h4km4k/esp_frequency-converter_controller/Esp32/favicon.h

#ifndef FAVICON_H
#define FAVICON_H

#include <stdint.h>
#include <pgmspace.h>

const uint8_t favicon_png[] PROGMEM = {
0x89, 0x50, 0x4E, 0x47, 0x0D, 0x0A, 0x1A, 0x0A, 0x00, 0x00, 0x00, 0x0D, 0x49, 0x48, 0x44, 0x52, 
0x00, 0x00, 0x00, 0xC0, 0x00, 0x00, 0x00, 0xC0, 0x08, 0x06, 0x00, 0x00, 0x00, 0x52, 0xDC, 0x6C, 
0x07, 0x00, 0x00, 0x1A, 0x24, 0x49, 0x44, 0x41, 0x54, 0x78, 0x5E, 0xED, 0x9D, 0x09, 0x78, 0x14, 
0x45, 0xFA, 0x87, 0x7F, 0x95, 0x73, 0x72, 0xDF, 0xF7, 0xC1, 0x91, 0x84, 0x40, 0x08, 0x88, 0xB6, 
0xBB, 0x02, 0x23, 0x02, 0x72, 0x23, 0xA0, 0x03, 0x4C, 0x70, 0x55, 0xC4, 0x1B, 0x2F, 0x76, 0xD7, 
0x7B, 0xFF, 0xAB, 0xAE, 0xEC, 0xBA, 0x2E, 0x2A, 0xA2, 0xAB, 0x5C, 0x8B, 0x08, 0x12, 0x59, 0x58, 
0xC8, 0x40, 0x7B, 0x8C, 0x1C, 0x82, 0xE7, 0x8A, 0x07, 0xBB, 0xDA, 0xB8, 0x28, 0x67, 0x06, 0x88, 
0x10, 0x42, 0x98, 0x10, 0xC8, 0x9D, 0xC9, 0x35, 0xFD, 0x7F, 0xBA, 0x43, 0x34, 0x38, 0x9D, 0xCC, 
0x24, 0x99, 0x49, 0x57, 0xD2, 0xF5, 0x3E, 0x4F, 0x9E, 0x89, 0x32, 0x99, 0xA9, 0xFE, 0xBA, 0xDE, 
0xFE, 0xAA, 0xAA, 0xAB, 0xAA, 0x09, 0x3A, 0x80, 0x08, 0x91, 0xC0, 0x68, 0x0A, 0x45, 0xA3, 0x3D, 
0x0E, 0xBE, 0x64, 0x08, 0x44, 0x32, 0x0E, 0x40, 0x36, 0x44, 0xF4, 0x03, 0x41, 0x18, 0x80, 0x20, 
0x00, 0x5E, 0x1D, 0xF8, 0x48, 0x06, 0xA3, 0xA3, 0xD8, 0x01, 0x54, 0x03, 0x28, 0x07, 0x50, 0x00, 
0x91, 0xFC, 0x00, 0x22, 0x7E, 0x84, 0x46, 0xFB, 0x7E, 0xF8, 0x78, 0x9D, 0x85, 0xC9, 0x58, 0x41, 
0x40, 0x44, 0x57, 0x3F, 0x94, 0xB8, 0xF2, 0xC6, 0x8B, 0x15, 0x3F, 0x05, 0x44, 0x9C, 0x0A, 0x91, 
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
0x5F, 0x48, 0x19, 0xA0, 0x08, 0x44, 0x4C, 0x60, 0x01, 0x61, 0x68, 0x0E, 0x91, 0x9C, 0x21, 0xE2, 
0xEC, 0xBC, 0x6A, 0x10, 0x04, 0x6A, 0xEE, 0xE0, 0x19, 0x0C, 0x11, 0x35, 0x44, 0xCC, 0xC9, 0x6B, 
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
};

const unsigned int favicon_png_len = sizeof(favicon_png);

#endif
